Chesters-CZ/Enhanced-power-button/arduino/cízí věci/ostatní/ArduinoHIDKeyboard/ArduinoHIDKeyboard/Keycode/Keyboard.png

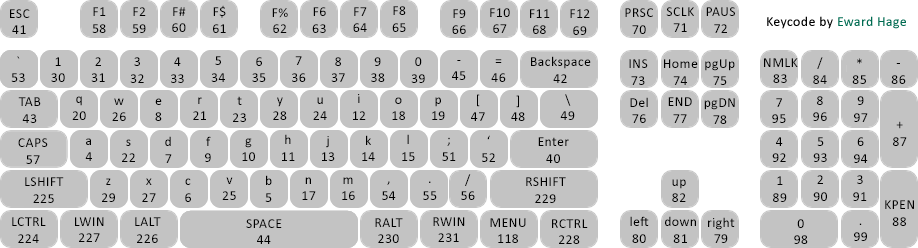
arduino/cízí věci/ostatní/ArduinoHIDKeyboard/ArduinoHIDKeyboard/Keycode/Keyboard.png
