Chesters-CZ/Enhanced-power-button/arduino/startup sounds/kahoots/coverart.jpg

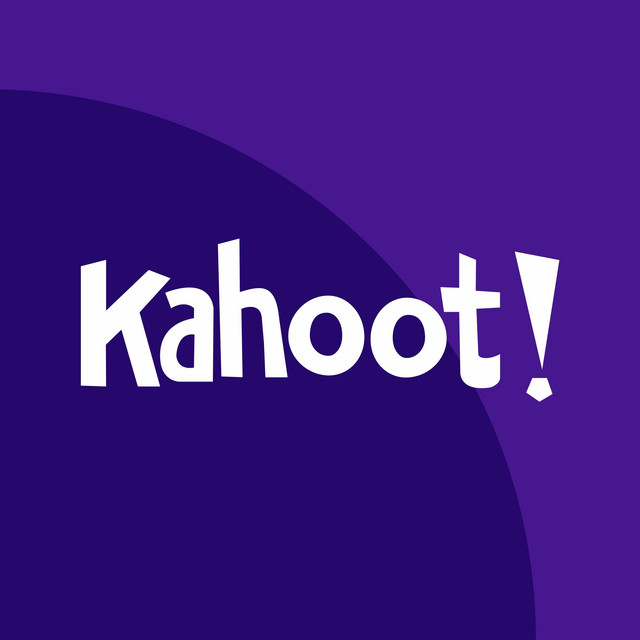
arduino/startup sounds/kahoots/coverart.jpg
