Chesters-CZ/Enhanced-power-button/fotky a schémata/20230131_195123(0).jpg

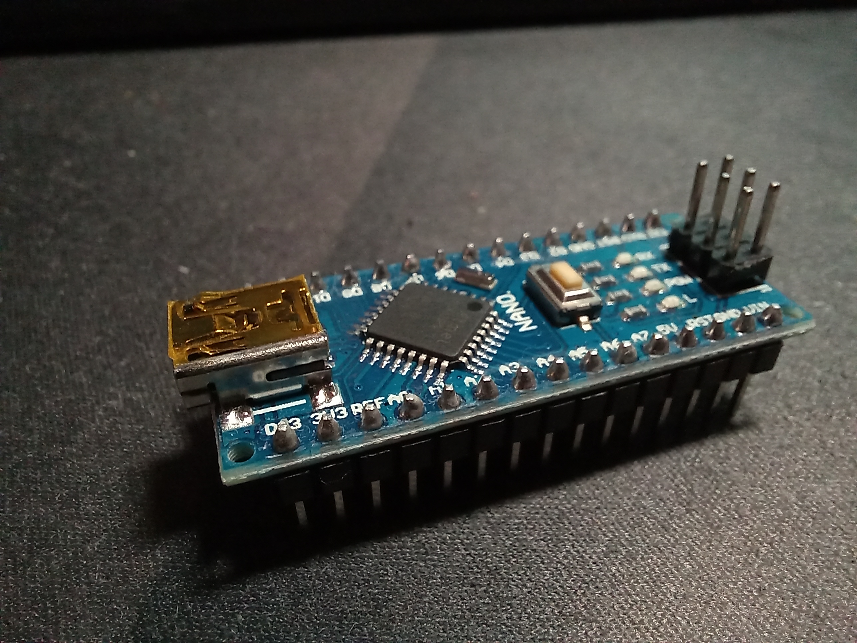
fotky a schémata/20230131_195123(0).jpg
