Chesters-CZ/Enhanced-power-button/fotky a schémata/AES grid.png

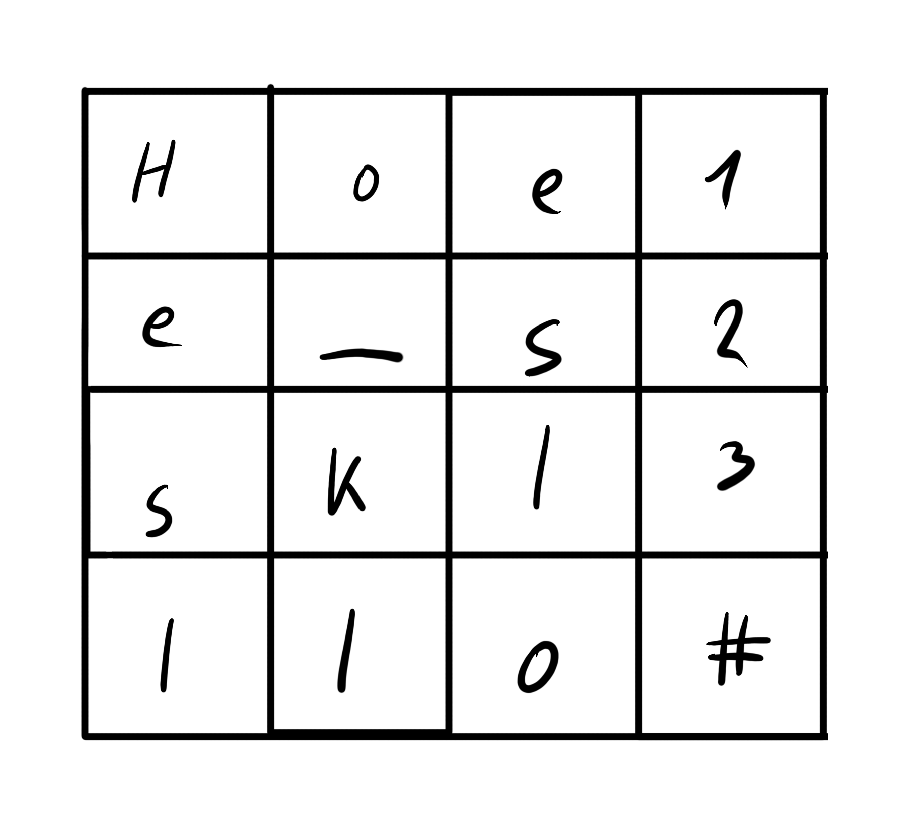
fotky a schémata/AES grid.png
