Chesters-CZ/Enhanced-power-button/fotky a schémata/concept art/20210127_220451.jpg

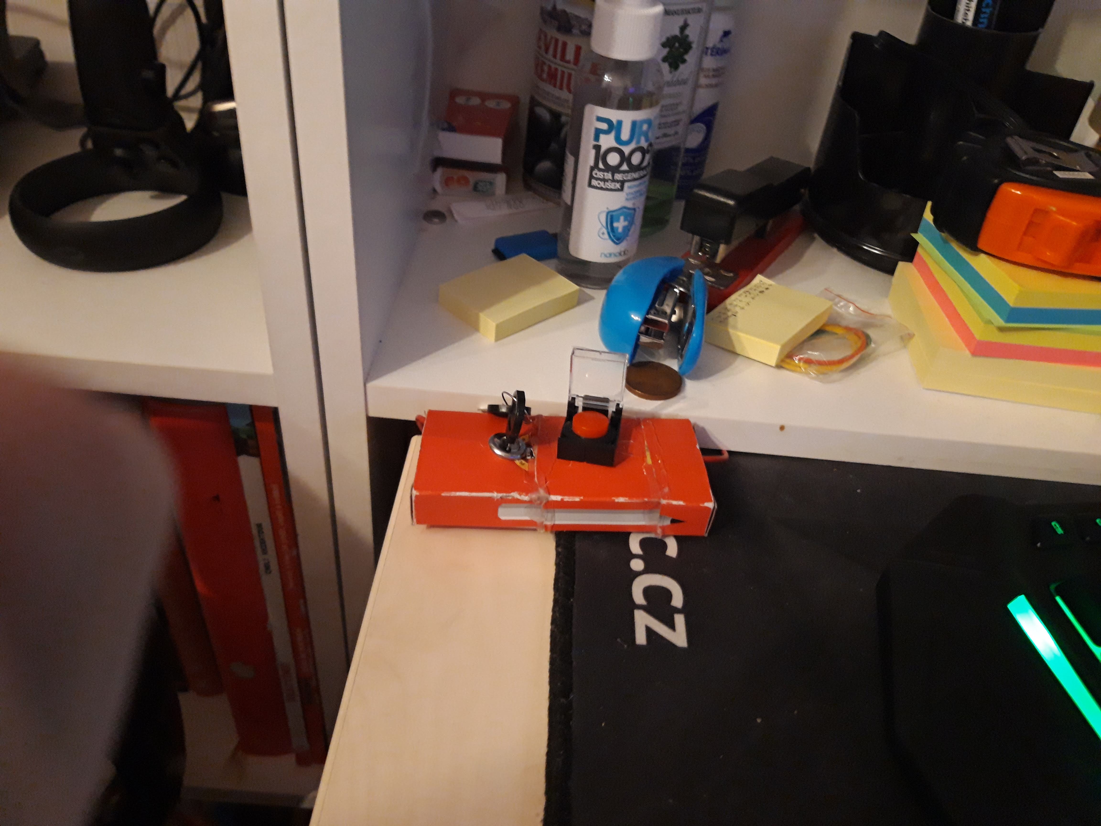
fotky a schémata/concept art/20210127_220451.jpg
