Chesters-CZ/Enhanced-power-button/fotky a schémata/concept art/20210127_220452.jpg

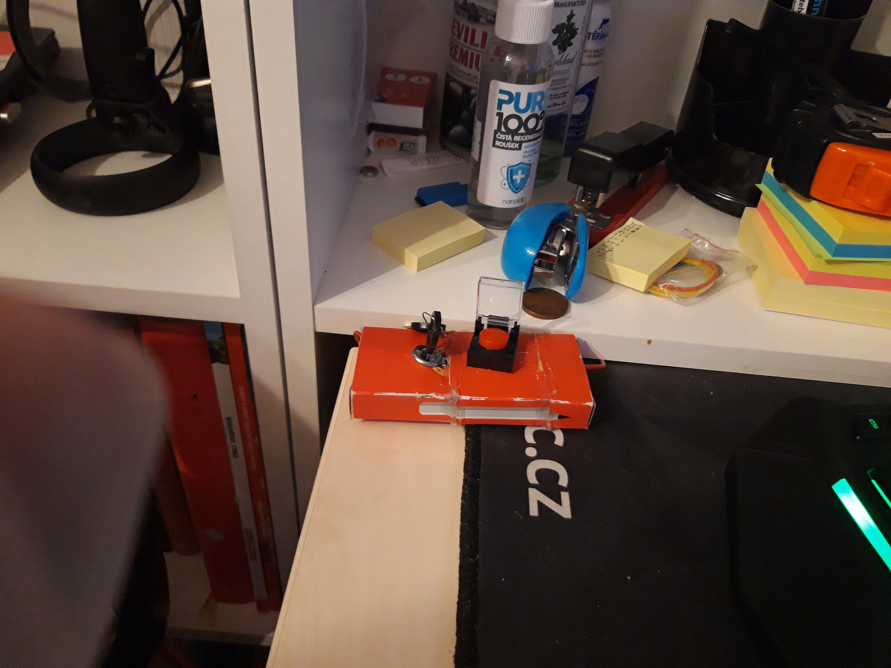
fotky a schémata/concept art/20210127_220452.jpg
