Chesters-CZ/Enhanced-power-button/fotky a schémata/concept art/20220127_121930.jpg

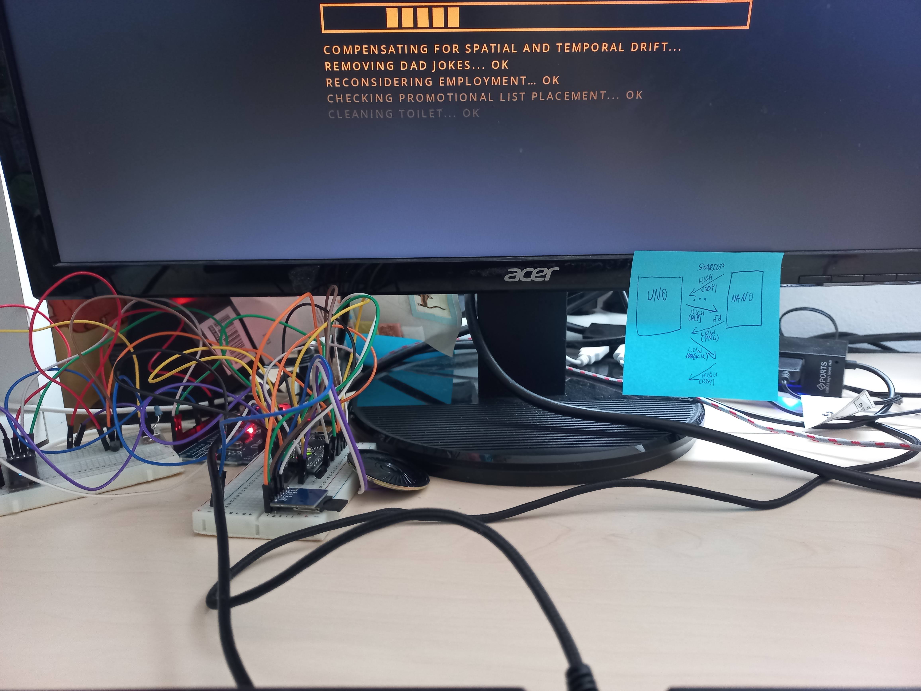
fotky a schémata/concept art/20220127_121930.jpg
