Chesters-CZ/Enhanced-power-button/fotky a schémata/concept art/20220902_204653.jpg

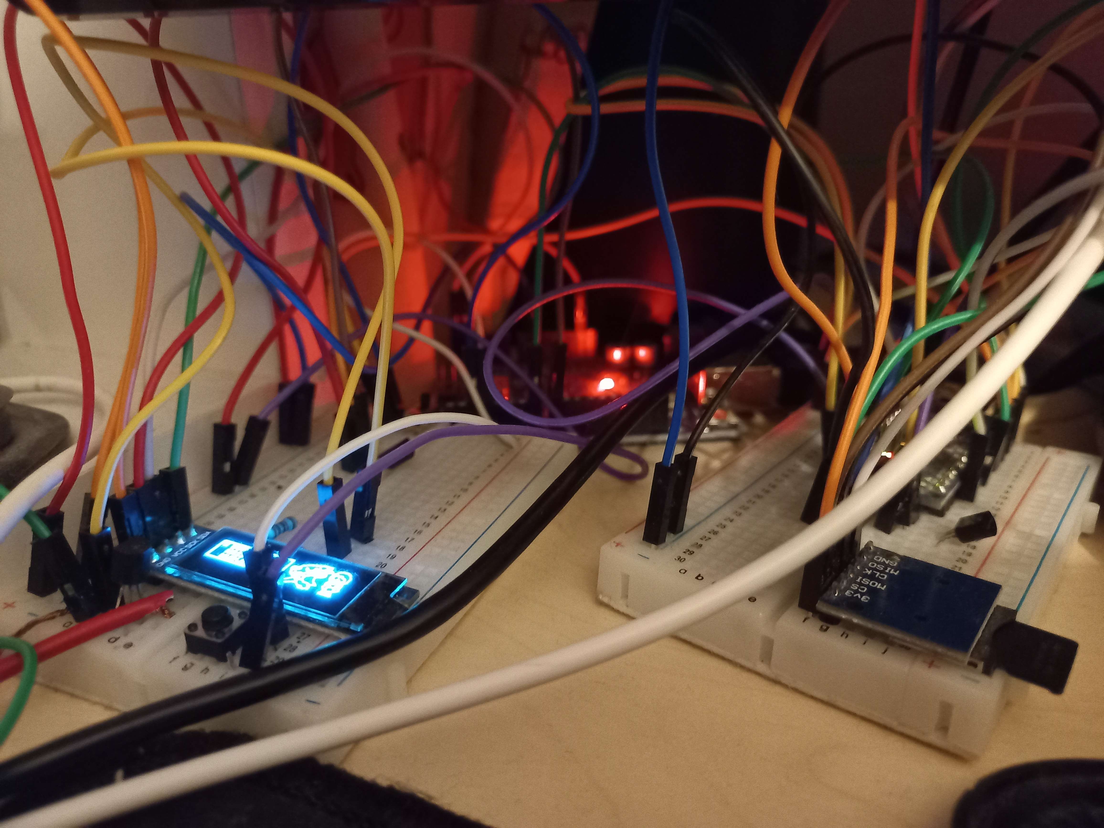
fotky a schémata/concept art/20220902_204653.jpg
