Chesters-CZ/Enhanced-power-button/fotky a schémata/Můj comm example.png

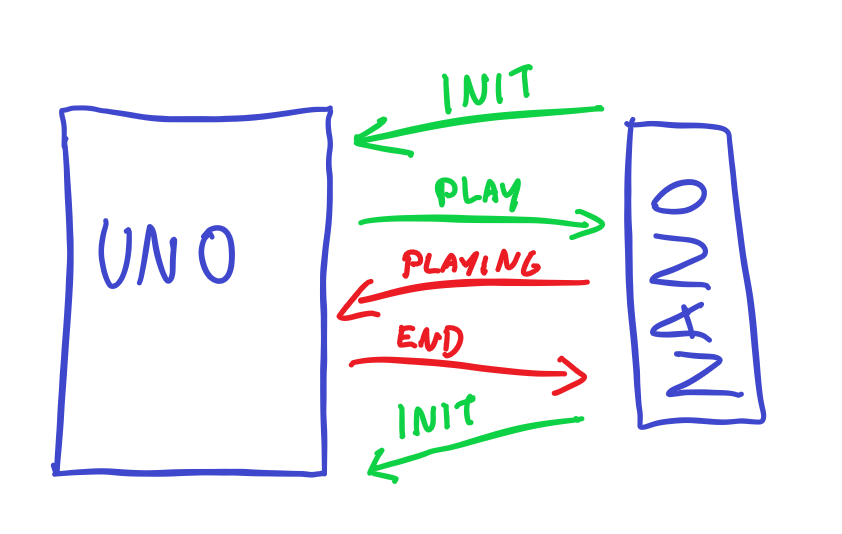
fotky a schémata/Můj comm example.png
