Chesters-CZ/Enhanced-power-button/fotky a schémata/Můj protokol.png

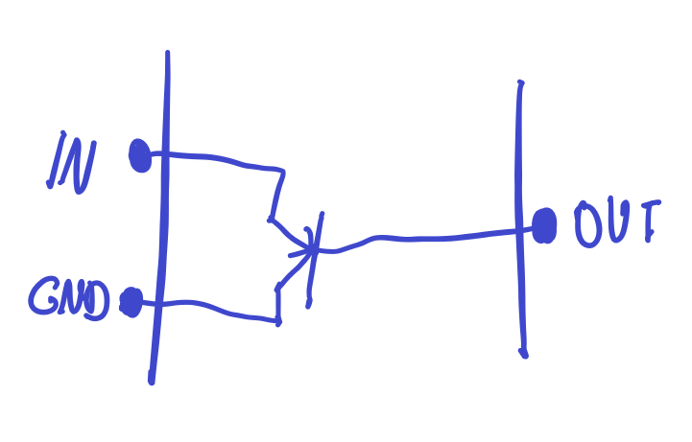
fotky a schémata/Můj protokol.png
