Chesters-CZ/Enhanced-power-button/fotky a schémata/schema s třema inama.jpg

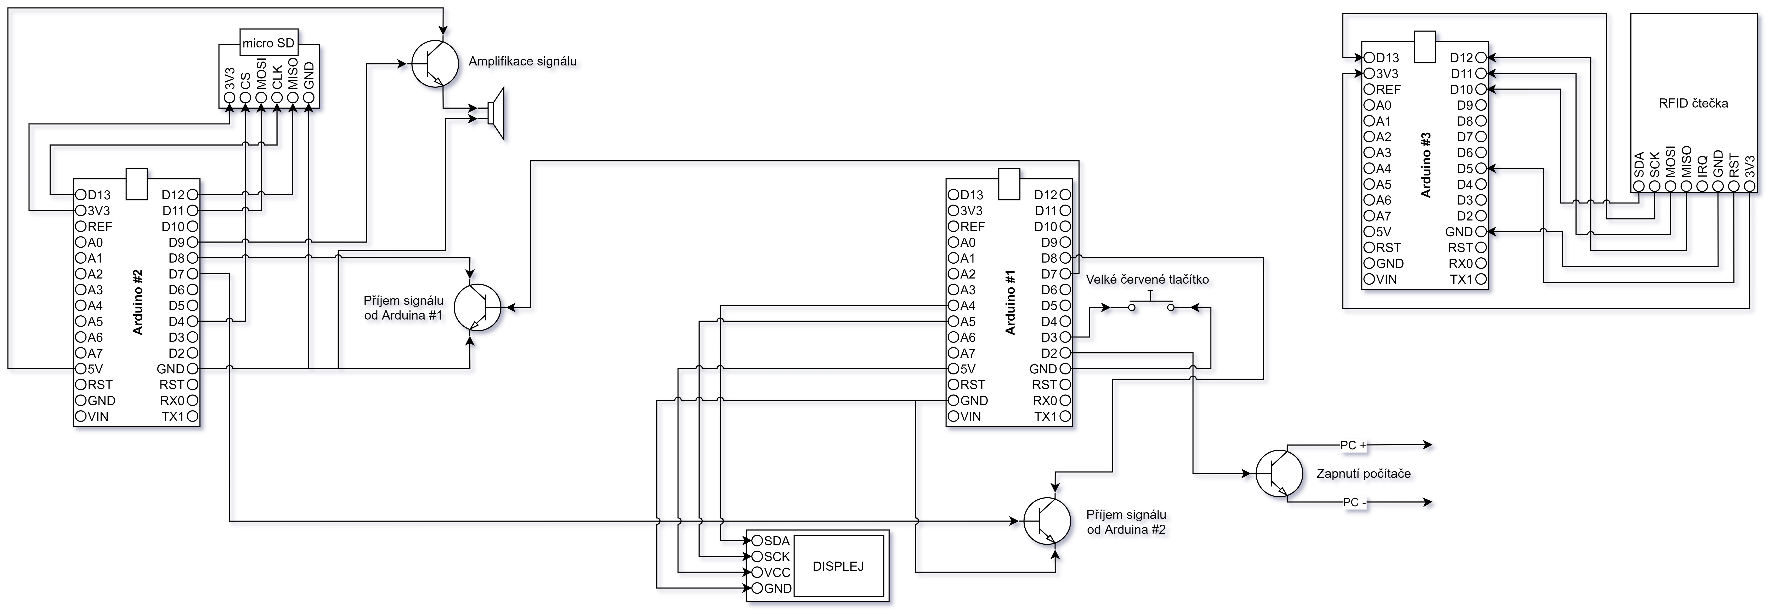
fotky a schémata/schema s třema inama.jpg
