Chesters-CZ/Enhanced-power-button/fotky a schémata/Stefano the tactical ostrich w name.png

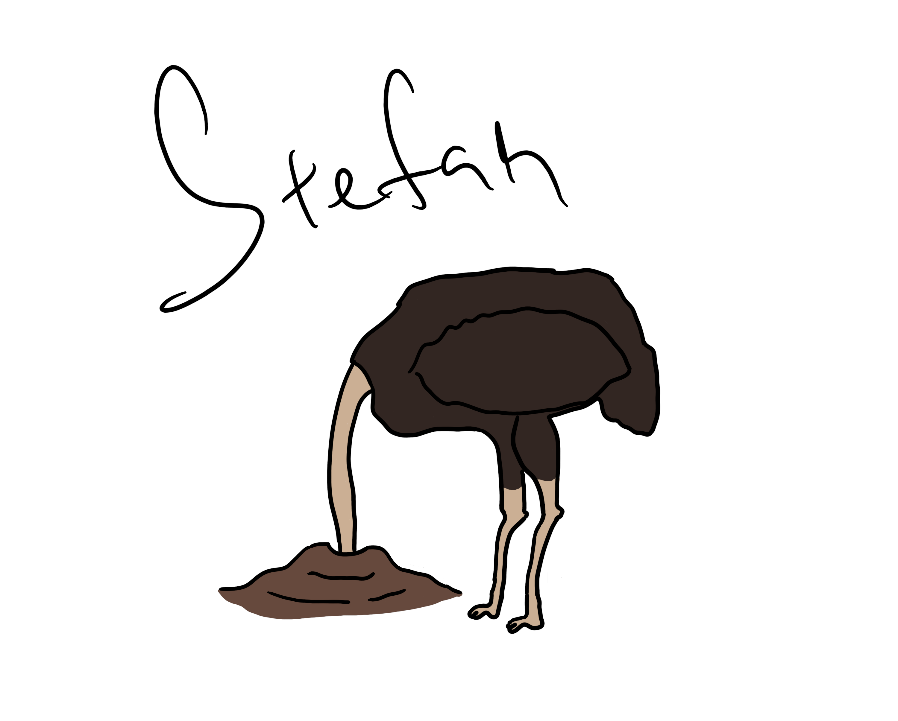
fotky a schémata/Stefano the tactical ostrich w name.png
