Chesters-CZ/Enhanced-power-button/fotky a schémata/Stefano the tactical ostrich.png

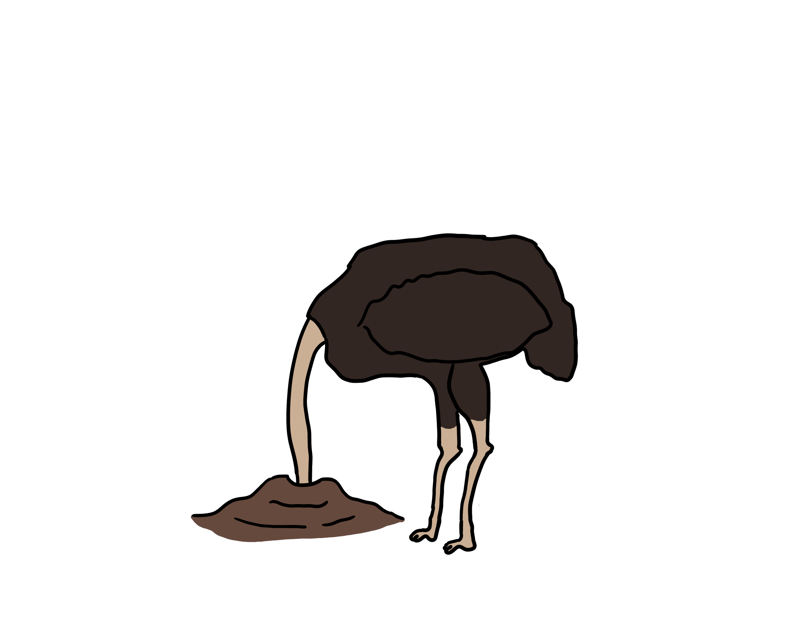
fotky a schémata/Stefano the tactical ostrich.png
