Chesters-CZ/Enhanced-power-button/fotky a schémata/Ti protokol.png

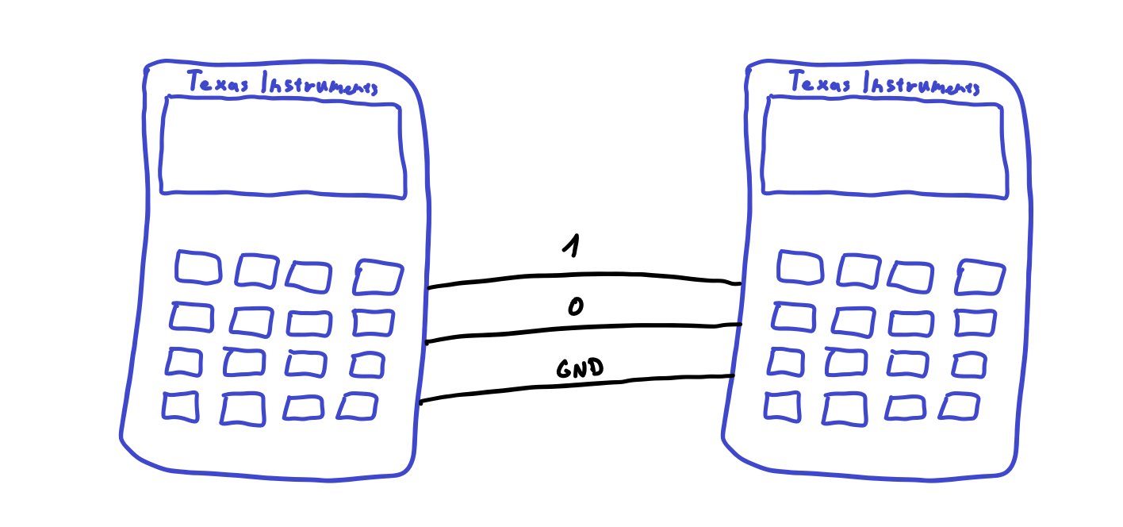
fotky a schémata/Ti protokol.png
