Chesters-CZ/Enhanced-power-button/fotky a schémata/tranzistor.png

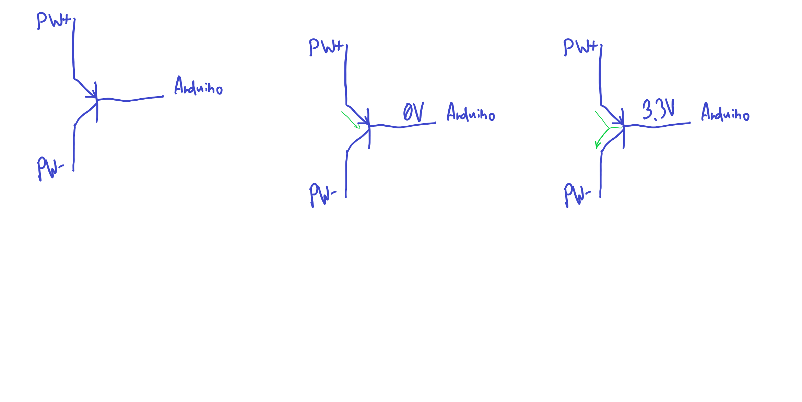
fotky a schémata/tranzistor.png
