Chesters-CZ/Enhanced-power-button/fotky a schémata/základ krabičky.png

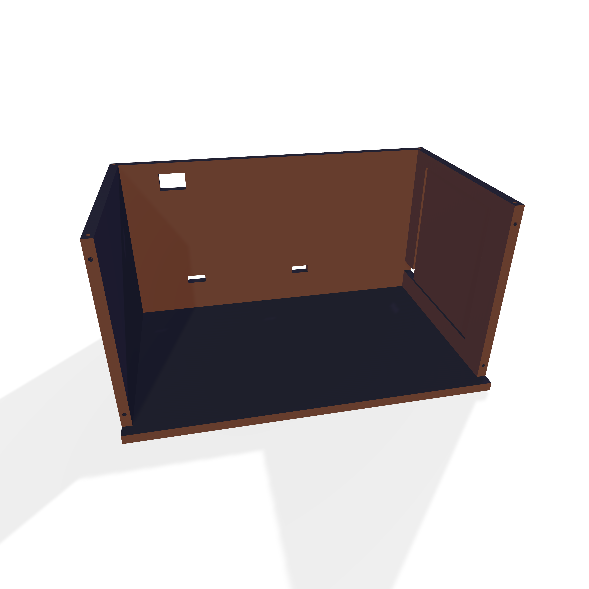
fotky a schémata/základ krabičky.png
