Chesters-CZ/Enhanced-power-button/python/friendship ENDED.png

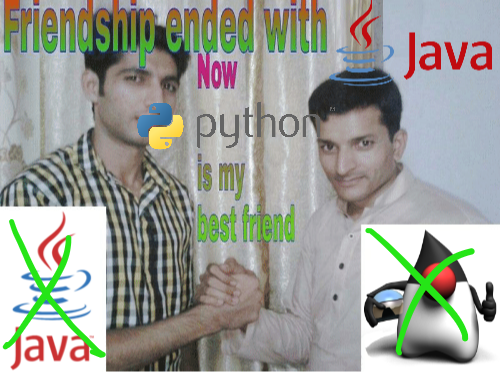
python/friendship ENDED.png
