Chesters-CZ/Enhanced-power-button/arduino/project fily/encrypt_spaniakos/encrypt_spaniakos.ino

#include <AES.h>
#include <AES_config.h>
#include "base64.hpp"
#include "EasyMFRC522.h"


AES aes;

EasyMFRC522 rfid(10, 5);

// !!! DŮLEŽITÉ !!!
// Před použitím změňte heslo, šifrovací klíč a
// inicializační vektor na vlastní hodnoty.

// Heslo k zašifrování
byte plain[] = "UltraSuperSecret69_!";

// Šifrovací klíč           "Sem je to AES128"sem 192"sem 256"
byte *key = (unsigned char*)"4428472B4B625065";

// Inicializační vektor
unsigned long long int my_iv = 22176790;

int plainLength = sizeof(plain) - 1; // nepočítat null terminator
int padedLength = plainLength + N_BLOCK - plainLength % N_BLOCK; // ???

int block = 1;

byte noIn = 2;
byte yesPin = 3;
byte noPin = 4;
byte yesIn = 6;

bool answer;

void setup() {
  Serial.begin (9600);
  while (!Serial) {
    ; // wait for serial port to connect. Needed for Leonardo only
  }
  delay(500);
  rfid.init();
}

void loop() {
  pinMode(noIn, OUTPUT);
  pinMode(yesIn, OUTPUT);
  pinMode(yesPin, INPUT_PULLUP);
  pinMode(noPin, INPUT_PULLUP);

  digitalWrite(noIn, HIGH);
  digitalWrite(yesIn, HIGH);

  Serial.println("PŘIPRAVUJI SE NA ZAPSÁNÍ HESLA...");
  Serial.println("ZAMKNE TENTO ČIP POČÍTAČ PO PŘERUŠENÍ SPOJENÍ?");
  Serial.println("TLAČÍTKO U ZELENÉ LED: ANO");
  Serial.println("TLAČÍTKO U ČERVENÉ LED: NE");
  Serial.println();

  while (digitalRead(yesPin) && digitalRead(noPin)) {
  }

  if (!digitalRead(yesPin)) {
    answer = true;
    digitalWrite(noIn, LOW);
    Serial.println("ČIP ZAMKNE POČÍTAČ PO PŘERUŠENÍ SPOJENÍ");
  } else if (!digitalRead(noPin)) {
    answer = false;
    digitalWrite(yesIn, LOW);
    Serial.println("ČIP NEZAMKNE POČÍTAČ PO PŘERUŠENÍ SPOJENÍ");
  } else {
    Serial.println("STALA SE CHYBA");
    return;
  }

  String y = key;
  if (y.length() == 16) {
    sifrujAZapis(128, answer);
  }
  else if (y.length() == 24) {
    sifrujAZapis(192, answer);
  }
  else if (y.length() == 32) {
    sifrujAZapis(256, answer);
  }
  else {
    Serial.print("ZVOLENA NEPLATNÁ DÉLKA KLÍČE (");
    Serial.print(sizeof(key));
    Serial.println(")");
    Serial.println("PODPOROVANÉ DÉLKY KLÍČE JSOU:");
    Serial.println("16 ZNAKŮ PRO AES128 (VYSOKÁ ÚROVEŇ ZABEZPEČENÍ)");
    Serial.println("24 ZNAKŮ PRO AES192 (VELMI VYSOKÁ ÚROVEŇ ZABEZPEČENÍ)");
    Serial.println("32 ZNAKŮ PRO AES256 (EXTRÉMNĚ VYSOKÁ ÚROVEŇ ZABEZPEČENÍ)");

    while (true) {
    }
  }


  digitalWrite(noIn, LOW);
  digitalWrite(yesIn, LOW);

  delay(3000);
}

void sifrujAZapis (int bits, bool willLogOffOnRemoved)
{
  aes.iv_inc();
  byte iv [N_BLOCK] ;
  byte plain_p[padedLength];
  byte cipher [padedLength] ;
  byte check [padedLength] ;
  unsigned long ms = micros ();
  aes.set_IV(my_iv);
  aes.get_IV(iv);
  aes.do_aes_encrypt(plain, plainLength, cipher, key, bits, iv);
  Serial.print("Encryption took: ");
  Serial.println(micros() - ms);

  char pass64[64] = {0};
  byte b64Length = encode_base64(cipher, padedLength, pass64);

  for (int i = b64Length; i < 64; i++) {
    pass64[i] = '=';
  }

  Serial.println(pass64);

  Serial.println();
  Serial.println(F("READY TO WRITE"));

  bool success = false;
  do {
    // returns true if a Mifare tag is detected
    success = rfid.detectTag();
    delay(50); //0.05s
  } while (!success);


  Serial.println(F("WRITING PASSWORD... "));
  block = rfid.writeFile(1, "Pass", (byte*)pass64, b64Length);
  if (block >= 0) {
    Serial.println(F("WRITING SUCCESSFUL"));
    Serial.print(block);
    Serial.println(F("WRITING LENGTH... "));
    String s = plain;
    block = rfid.writeFile(40, "PLen", (byte*)String(s.length()).c_str(), sizeof(String(b64Length)));

    if (block >= 0) {
      Serial.println(F("WRITING SUCCESSFUL"));
      Serial.print(block);

      Serial.println(F("WRITING LOGOFF PREFERENCE... "));

      if (willLogOffOnRemoved) {
        block = rfid.writeFile(50, "LogOff", "true", sizeof("true"));
      } else {
        block = rfid.writeFile(50, "LogOff", "fals", sizeof("fals"));
      }

      if (block >= 0) {
        Serial.println(F("WRITING SUCCESSFUL"));
        Serial.print(block);
      }  else {
        Serial.print(F("WRITING FAILED"));
        Serial.print(block);
      }

    } else {
      Serial.print(F("WRITING FAILED"));
      Serial.print(block);
    }
  } else {
    Serial.print(F("WRITING FAILED"));
    Serial.print(block);
  }

  rfid.unselectMifareTag();

  /*
    ms = micros ();
    aes.set_IV(my_iv);
    aes.get_IV(iv);
    aes.do_aes_decrypt(cipher,padedLength,check,key,bits,iv);
    Serial.print("Decryption took: ");
    Serial.println(micros() - ms);
    printf("\n\nPLAIN :");
    aes.printArray(plain,(bool)true);
    printf("\nCIPHER:");
    aes.printArray(cipher,(bool)false);
    printf("\nCHECK :");
    aes.printArray(check,(bool)true);
    printf("\nIV    :");
    aes.printArray(iv,16);
  */
  Serial.println("\n============================================================\n");
}
